EugenePY/A60/Photo Shoots/9702984b-9b6b-48a5-8010-a4bd6302d801.jpg

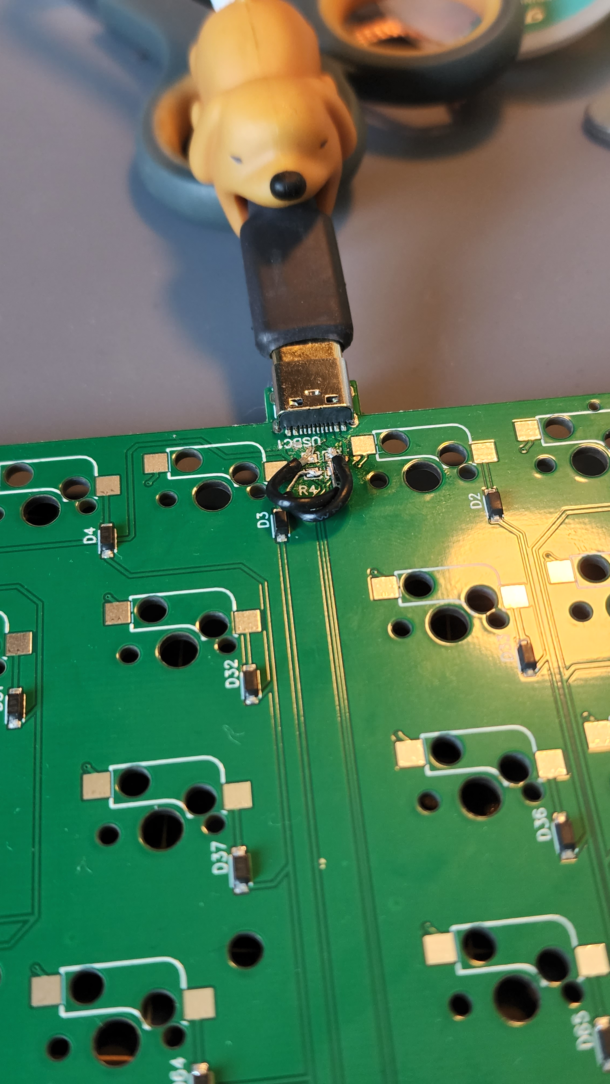
Photo Shoots/9702984b-9b6b-48a5-8010-a4bd6302d801.jpg
