EugenePY/A60/Photo Shoots/20221017_013522.jpg

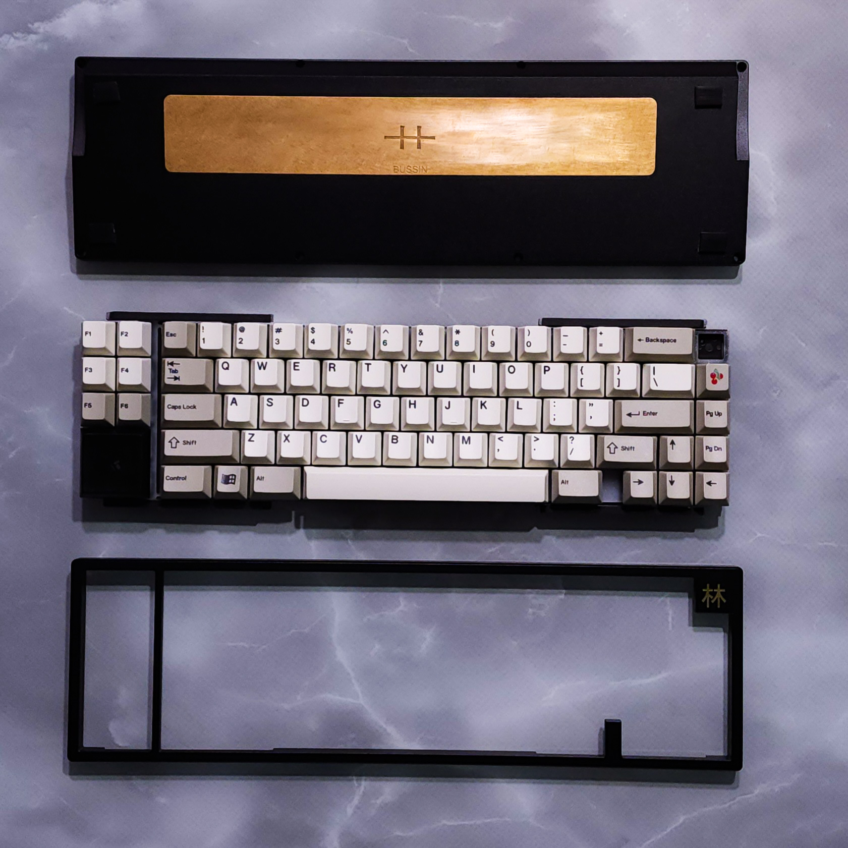
Photo Shoots/20221017_013522.jpg
