EugenePY/A60/Photo Shoots/mmexport1660487531319.png

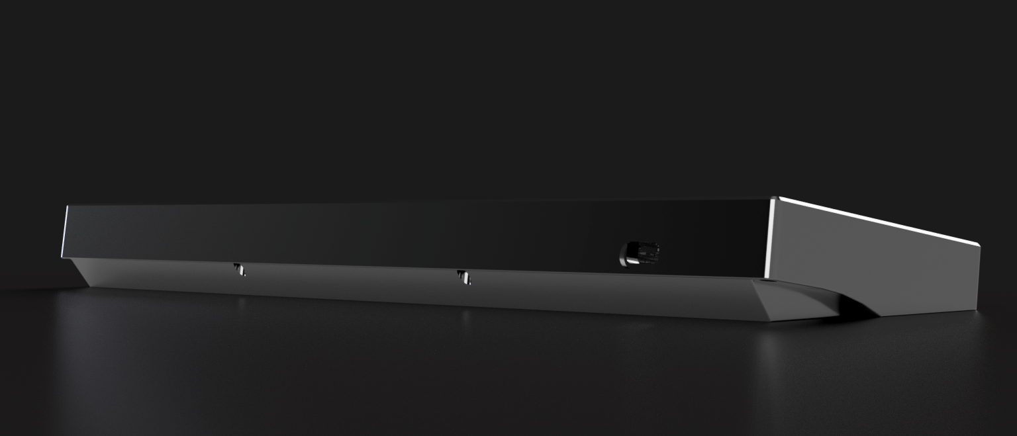
Photo Shoots/mmexport1660487531319.png
