EugenePY/A60/Photo Shoots/mmexport1660487534561.png

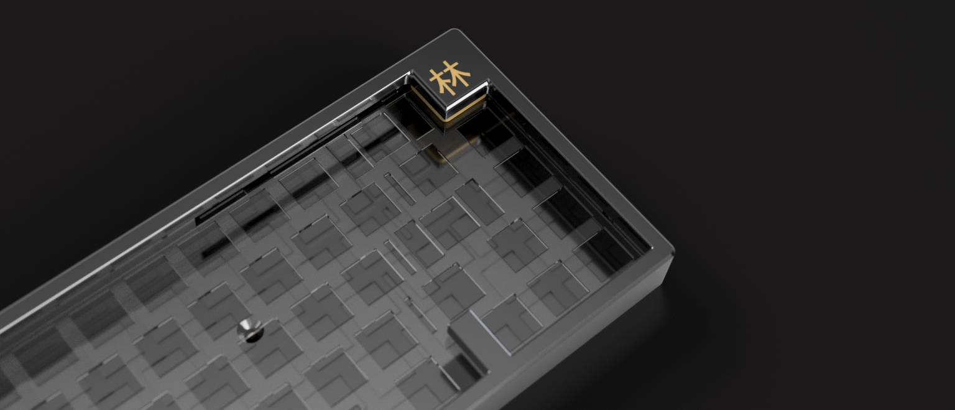
Photo Shoots/mmexport1660487534561.png
