EugenePY/A60/Photo Shoots/mmexport1660487536931.png

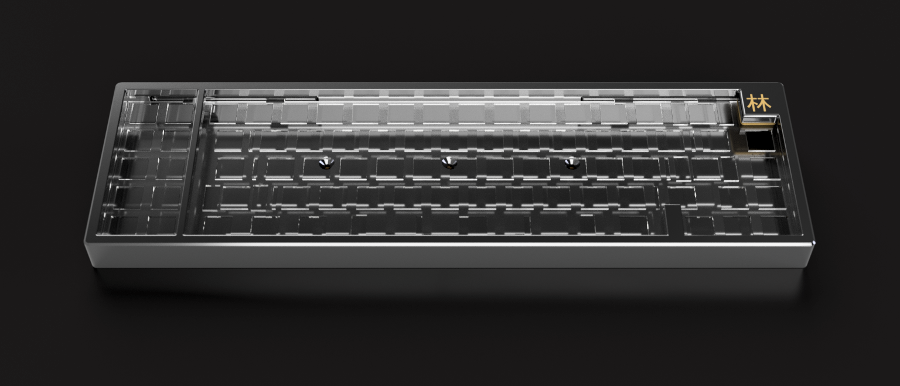
Photo Shoots/mmexport1660487536931.png
