EugenePY/A60/Photo Shoots/wx_camera_1662044980976.jpg

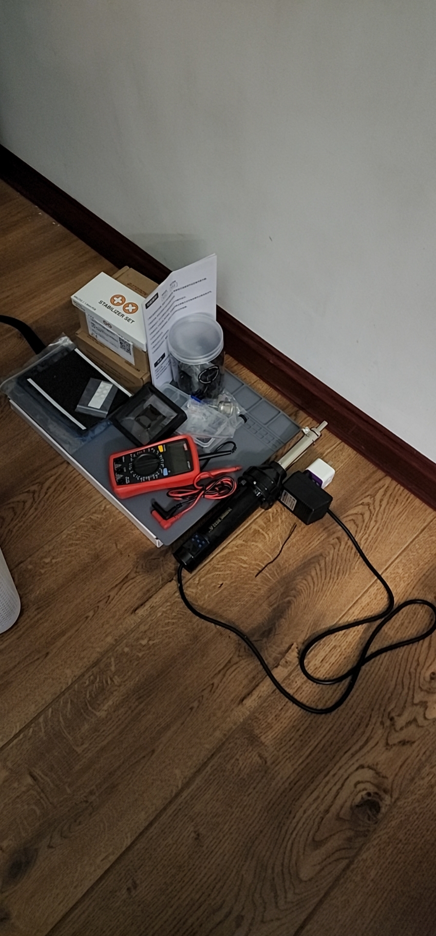
Photo Shoots/wx_camera_1662044980976.jpg
