EugenePY/A60/Photo Shoots/wx_camera_1665747350265.jpg

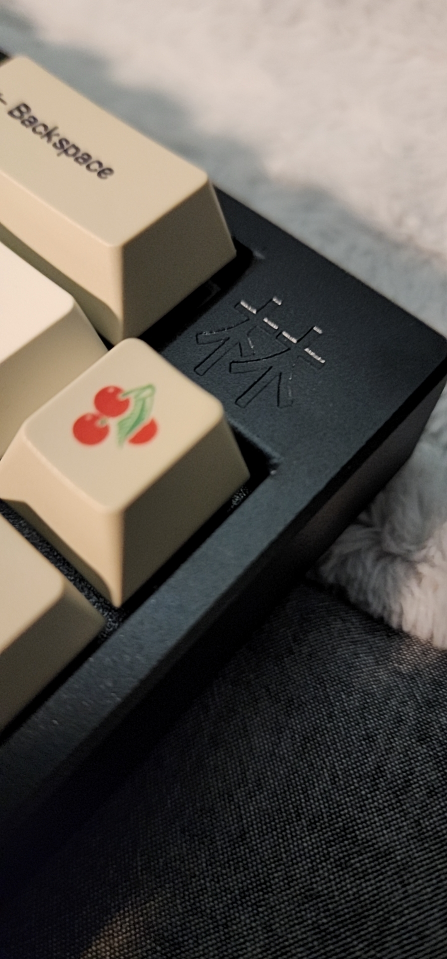
Photo Shoots/wx_camera_1665747350265.jpg
