EugenePY/A60/Photo Shoots/676dc1ad-e77f-421f-adf9-7bc19cab7afc.jpg

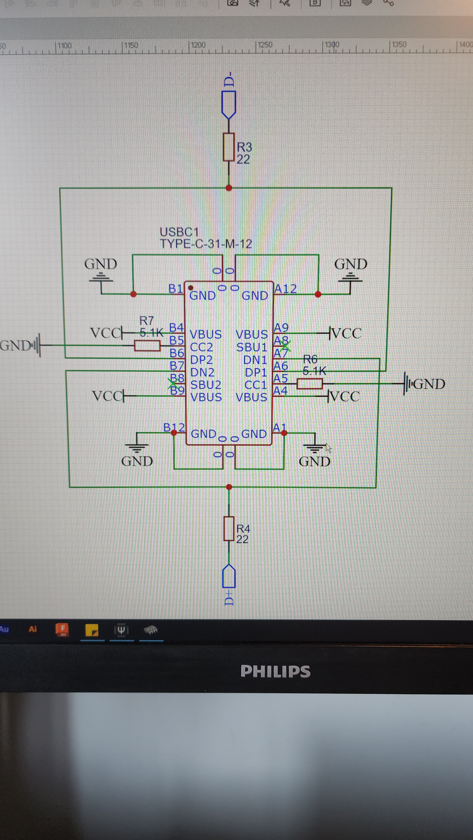
Photo Shoots/676dc1ad-e77f-421f-adf9-7bc19cab7afc.jpg
